1freemiracle/budcure/arduino code/Cannaster/FreeMonoBold12pt7b.h

// Created by https://oleddisplay.squix.ch/ Consider a donation
// In case of problems make sure that you are using the font file with the correct version!
const char Bold[] PROGMEM = {
	0x10, // Width: 16
	0x11, // Height: 17
	0x20, // First Char: 32
	0xE0, // Numbers of Chars: 224

	// Jump Table:
	0xFF, 0xFF, 0x00, 0x05,  // 32:65535
	0x00, 0x00, 0x0B, 0x06,  // 33:0
	0x00, 0x0B, 0x10, 0x07,  // 34:11
	0x00, 0x1B, 0x1F, 0x0C,  // 35:27
	0x00, 0x3A, 0x1A, 0x0A,  // 36:58
	0x00, 0x54, 0x29, 0x0E,  // 37:84
	0x00, 0x7D, 0x23, 0x0D,  // 38:125
	0x00, 0xA0, 0x07, 0x04,  // 39:160
	0x00, 0xA7, 0x0E, 0x06,  // 40:167
	0x00, 0xB5, 0x0E, 0x06,  // 41:181
	0x00, 0xC3, 0x14, 0x07,  // 42:195
	0x00, 0xD7, 0x1D, 0x0C,  // 43:215
	0x00, 0xF4, 0x08, 0x05,  // 44:244
	0x00, 0xFC, 0x0E, 0x06,  // 45:252
	0x01, 0x0A, 0x08, 0x05,  // 46:266
	0x01, 0x12, 0x0D, 0x05,  // 47:274
	0x01, 0x1F, 0x1A, 0x0A,  // 48:287
	0x01, 0x39, 0x17, 0x0A,  // 49:313
	0x01, 0x50, 0x17, 0x0A,  // 50:336
	0x01, 0x67, 0x1A, 0x0A,  // 51:359
	0x01, 0x81, 0x1A, 0x0A,  // 52:385
	0x01, 0x9B, 0x1A, 0x0A,  // 53:411
	0x01, 0xB5, 0x1A, 0x0A,  // 54:437
	0x01, 0xCF, 0x19, 0x0A,  // 55:463
	0x01, 0xE8, 0x1A, 0x0A,  // 56:488
	0x02, 0x02, 0x1A, 0x0A,  // 57:514
	0x02, 0x1C, 0x08, 0x06,  // 58:540
	0x02, 0x24, 0x08, 0x06,  // 59:548
	0x02, 0x2C, 0x1D, 0x0C,  // 60:556
	0x02, 0x49, 0x1D, 0x0C,  // 61:585
	0x02, 0x66, 0x1D, 0x0C,  // 62:614
	0x02, 0x83, 0x13, 0x08,  // 63:643
	0x02, 0x96, 0x26, 0x0E,  // 64:662
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
	0x00,0x00,0x00,0xF8,0x1F,0x00,0xF8,0x1F,0x00,0x80,0x00,0x00,0x80,0x00,0x00,0x80,0x00,0x00,0x80,0x00,0x00,0x80,0x00,0x00,0xF8,0x1F,0x00,0xF8,0x1F,	// 72
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
};
